X-ANONYMOUS-POWER-AMPLIFIER/X-B120W-4-LITE/3D-FOOTPRINTS/NTC.step

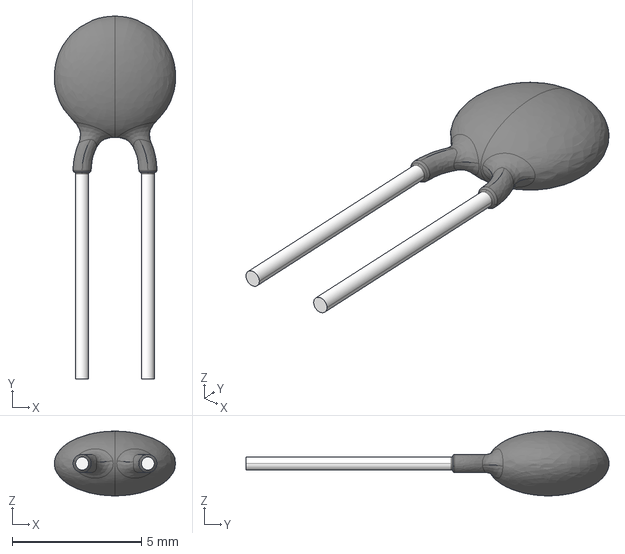
[picture p21: CAD file, 2026-05-12]
3D-FOOTPRINTS/NTC.step
4.70 x 14.0 x 2.50 mm
